JaphD/USB-C-PD-Smart-Power-Supply/Docs/Sim/TPS259470_EN_UVLO_MCU_Control.asc

R1: res; 2.2Meg
R3: res; 1k
R4: res; 100k
U1: T2N7002AK_G0_00
V1: voltage; 20; AC 0
V2: voltage; 3.3; AC 0
V3: voltage; PULSE(3.3 0 10m 1u 1u 20m 40m); AC 0
Named nets: 0, VBUS_PD, EN_UVLO, GATE, MCU_GPIO
.tran 0 100m 0 10u
